MartinD-CZ/BrymenConnector21/App/comport.cpp

/* comport.cpp
 *
 * Created on: Mar 7, 2022
 * Author: Martin Danek, martin@embedblog.eu
 */

#include "comport.h"

#include "proj_conf.h"
#include "hal_inc.h"
#include "main.h"
#include "version.h"

#include <ctype.h>

extern UART_HandleTypeDef huart2;
extern Request request;

static uint8_t rxData[16];
static char stdoutBuf[256];

void HAL_UARTEx_RxEventCallback(UART_HandleTypeDef *huart, uint16_t Size)
{
	if (huart->Instance == huart2.Instance)
	{
		request = (Request)tolower(rxData[0]);


		HAL_UARTEx_ReceiveToIdle_DMA(&huart2, rxData, sizeof(rxData));
	}
}

void comport::init()
{
	MX_USART2_UART_Init();
	HAL_UARTEx_ReceiveToIdle_DMA(&huart2, rxData, sizeof(rxData));
	setvbuf(stdout, stdoutBuf, _IOLBF, sizeof(stdoutBuf));		//use static buffer for printf
	printHelp();
}

void comport::printHelp()
{
	printf("\n\nBrymen 867/869 interface cable\nfor more info, see http://embedblog.eu/?p=830\n\n");
	printf("Firmware revision/commit: %s/%s\n", _V_BUILD_TAG, _V_COMMIT);
	printf("Available commands:\n");
	printf("F - Five samples per second\n");
	printf("   (note that the multimeter doesn't support this with both displays (AUX and MAIN) enabled)\n");
	printf("O - One sample per second\n");
	printf("S - Stop autosend\n");
	printf("D - read single Data\n");
	printf("R - toggle Raw data output\n");
	printf("E - save current settings to Eeprom\n");
	printf("H - prints out help & all available commands\n");
}

extern "C" int _write(int file, char* ptr, int len)
{
	auto status = HAL_UART_Transmit(&huart2, (uint8_t*)ptr, len, 100);

	if (status == HAL_OK)
		return len;
	else
		return 0;
}

void custom_assert(const char* file, uint32_t line)
{
	printf("ASSERT FAILED! File %s, line %u\n", file, (unsigned int)line);

	#if defined(DEBUG)
	__asm("bkpt 0");		//breakpoint instruction
	#endif
}
