MartinD-CZ/BrymenConnector21/App/comport.h

/* comport.h
 *
 * Created on: Mar 7, 2022
 * Author: Martin Danek, martin@embedblog.eu
 */

#ifndef COMPORT_H_
#define COMPORT_H_

namespace comport
{
	void init();
	void printHelp();
}



#endif /* COMPORT_H_ */
