MartinD-CZ/BrymenConnector21/App/proj_conf.h

/* proj_conf.h
 *
 * Created on: Mar 7, 2022
 * Author: Martin Danek, martin@embedblog.eu
 */

#ifndef PROJ_CONF_H_
#define PROJ_CONF_H_

#include <stdint.h>

constexpr uint8_t EEPROM_VALID_FLAG = 0xC4;
constexpr uint8_t EEPROM_VALID_ADDR = 0x00;

constexpr uint8_t EEPROM_CONF_ADDR = 0x01;

constexpr uint_fast16_t CLOCK_DELAY_US = 100;

enum class Mode: uint8_t
{
	SEND_1HZ,
	SEND_5HZ,
	STOP
};

enum class Request: char
{
	NONE,
	SAVE_EEPROM = 'e',
	SET_MODE_1HZ = 'o',
	SET_MODE_5HZ = 'f',
	SET_MODE_STOP = 's',
	REQUEST_DATA = 'd',
	SET_RAW = 'r',
	GET_HELP = 'h',
};


#endif /* PROJ_CONF_H_ */
